shattori-criepi/omk/docs/design-principles.md

# 設計原則

## 1. この文書の目的

OMKは、一般的なWebアプリよりもハードウェア、通信、設置環境、長期運用の影響を強く受けます。本書は、個別の技術選定より長く維持する設計原則を定義します。

本書には長期的な設計方針も含み、すべてが現在の実装で満たされているわけではありません。実装済みの構成は[アーキテクチャ](developer/architecture.md)、保存形式・時刻・送信経路は[データ経路とMQTT仕様](developer/data-and-mqtt.md)を参照してください。現在は複数サービスで構成され、JSTのoffset付き時刻を保存し、Harvestへの送信はcollectorの保存完了と同期しません。Bルート固有CSVもJSONLと並行して保存します。

判断に迷った場合は、短期的にコード量が少ない方法よりも、次の優先順位を使います。

1. 計測データを失わない
2. 一部故障でも残りを動かす
3. 機器やベンダーを交換できる
4. 実機なしで開発・検証できる
5. 運用者が状態と原因を理解できる
6. 人間と生成AIが安全に変更できる

## 2. OMKの価値を維持する

OMKの価値は、多数のセンサを搭載すること自体ではありません。目的に応じて必要な計測機能を選択し、住宅への負担や設置コストを抑えながら長期間計測できることです。

### 原則

- センサ数を増やす前に、目的達成に必要かを確認する
- 設置作業、故障箇所、保守作業が増えることをコストとして扱う
- 構成は設定で選択できるようにする
- 使わない機能が他機能の起動を妨げないようにする
- UIは利用者に不要な操作を要求しない

## 3. モジュラーモノリスを優先する

OMKの初期・中期規模では、ネットワーク越しに分散した多数のサービスより、明確に分割された一つのアプリケーションの方が理解・検証・配備しやすいと判断します。

現在はこの判断基準に沿って、4つのComposeサービスとデバイス操作等のhost serviceに分割しています。この節は一つのプロセスへ統合済みであることを意味しません。

### 守ること

- モジュールごとに公開APIを定義する
- 他モジュールの内部ファイルを直接importしない
- 循環依存を作らない
- 一つの巨大な`utils`、`common`、`manager`へ責務を集めない
- コンテナ分割をコードの責務分割の代わりにしない
- コンテナを増やす場合は運用上の理由を記録する

### 分割の判断

別プロセス／別コンテナにする候補は、次の条件を持つものです。

- ランタイムが異なる
- 特殊なデバイス権限が必要
- 独立再起動に価値がある
- 障害やセキュリティを分離する必要がある

## 4. ハードウェアは交換可能なアダプタにする

### 原則

- ドメイン層はUSB、Bluetooth、Wi-SUN、GPIO、MQTTを知らない
- ベンダーSDKの型をアダプタ外へ出さない
- すべての実機ドライバにモックまたはシミュレータを用意する
- ドライバは共通`Measurement`を出力する
- ドライバの起動、停止、再接続、ヘルス確認を共通化する
- デバイス探索と計測処理を分ける

### 製品廃止への備え

機器の型番やSDKが廃止されることを例外ではなく通常のライフサイクルとして扱います。

- 型番をドメイン名やmetric名へ埋め込まない
- 設定でドライバ実装を選択する
- 通信プロトコルに対する契約テストを残す
- 実機がなくても再現できるサンプルデータを保存する
- 代替機器の評価結果は該当する`hardware/`またはコンポーネントREADMEへ記録し、確認済みの対応範囲は[対応機器](user/supported-devices.md)へ反映する
- 特定ベンダー機能へ依存する場合は理由と代替案を記録する

## 5. 取得と保存を分離し、JSONLを一次保存にする

各データ取得処理はMQTTへpublishし、汎用collectorがJSONLへ一次保存する。JSONLへの保存ではセンサ別の列定義へ展開せずpayloadを保持する。ただし現行collectorは保存前のBLE経路選択と、表示用latest cacheの抽出・互換出力も担う。JSONLは最終分析形式ではなく、CSV、分析、可視化、DB化、外部送信の入力となる生の保存形式である。

```text
Data acquisition
        ↓
MQTT internal data bus
        ↓
Generic collector
        ↓
JSONL primary storage
        ↓
CSV / analysis / visualization / external delivery
```

### 原則

- 取得と保存を分離し、MQTTを内部データバスとして使う
- topicは`omk/<device_id>/<data_type>`を基本とする
- collectorは`omk/#`を購読し、受信時刻・topic・payload等を保存する
- payloadの測定項目が増減してもcollectorを変更しない
- センサ固有の処理をcollectorへ持ち込まない
- CSVは一次保存ではなく、JSONLから生成する派生データとする

## 6. オフラインを通常状態として設計する

LTE、Wi-Fi、クラウド、MQTTは一時的に切断されます。通信断を例外処理だけで済ませず、通常運用の一部として設計します。

### 原則

- 外部送信より先にローカル保存する
- Outbox方式で未送信データを管理する
- 再送は指数バックオフと上限付きジッタを用いる
- 再送しても重複処理されない識別子を付ける
- キュー容量、ディスク使用量、最古未送信時刻を監視する
- 復旧後に自動追いつきできる
- 通信断中もUIで現在値と状態を確認できる

## 7. 一部故障を全体障害にしない

### 原則

- 一つのセンサ初期化失敗でプロセス全体を終了しない
- ドライバごとに状態と再接続処理を持つ
- 連続失敗をレート制限してログ出力する
- 依存していない機能は継続する
- 必須デバイスと任意デバイスを設定で区別する
- プロセス再起動に頼る前にコンポーネント単位で復旧する

### 状態の例

```text
starting → healthy → degraded → reconnecting → healthy
                     └──────────→ failed
```

`failed`でも、他コンポーネントが動作可能ならシステム全体のlivenessは維持します。

## 8. Raspberry Pi OSとコンテナの境界を保つ

DockerはすべてのOS設定を隠すためのものではありません。周辺機器を安定して使うため、ホストOSの責務を明確に残します。

### ホストOSへ置くもの

- カーネルドライバ
- Bluetoothデーモン
- LTE接続管理
- USB・シリアル認識
- udevルール
- ディスプレイ設定
- 時刻同期
- OS更新・再起動・電源管理
- Bルート通信（USBシリアル、PANA、認証）を実行するsystemdサービス

### コンテナへ置くもの

- 計測プロトコル
- データ変換
- 保存・送信
- API・UI
- ログ・ヘルスチェック
- モック・自動テスト

Bルート通信そのものは当面コンテナ化しない。Bルート取得値はMQTTへpublishし、他のセンサと同じ汎用collectorとJSONL一次保存へ集約する。既存の専用保存は、並行運用の検証が完了するまで維持する。

### 禁止事項

- 理由なく`privileged: true`を使う
- ホストのルートファイルシステムを広範囲にマウントする
- デバイスパスをコードへ直書きする
- ホスト設定変更をアプリ起動時に暗黙実行する

## 9. 設定とコードを分ける

設置場所ごとの差異は、原則としてコードの分岐ではなく設定で表現します。

### 設定に置くもの

- 有効なドライバ
- デバイスパス・Bluetoothアドレス
- 計測間隔
- サイト／デバイス識別子
- 保存期間
- 送信先種別とバッチサイズ
- UI表示項目
- ログレベル

### コードに置かないもの

- BルートID・パスワード
- APIキー
- SIM・利用者・設置場所を特定する秘密値
- 実在住宅固有の設定

設定は起動時にスキーマ検証し、誤りを分かりやすく報告します。

## 10. 時刻・単位・識別子を曖昧にしない

IoTデータでは、値そのものよりメタデータの曖昧さが後から大きな問題になります。

### 時刻

- 内部保存・通信はUTC
- UI表示時にタイムゾーン変換
- 観測時刻と受信時刻を区別
- NTP同期状態を監視
- 時計が不正なデータには品質フラグを付ける

### 単位

- 値と単位をセットで扱う
- 単位変換は正規化層で行う
- 変数名だけに単位情報を持たせない
- 同じmetricでは同じ基準単位を使う

### 識別子

- 表示名を主キーにしない
- `siteId`、`deviceId`、`sensorId`を分ける
- MACアドレス等の変更可能値へ過度に依存しない
- 再設置・機器交換時の識別方針を明示する

## 11. セキュリティとプライバシーを後付けにしない

住宅内の電力・環境データは、生活パターンを推定できる可能性があります。

### 原則

- 必要なデータだけを収集する
- 収集目的、保持期間、送信先を設定・文書で明示する
- 本番認証情報をGitへ入れない
- ログへ秘密値や生データを過剰に出さない
- MQTT、UI、APIの公開範囲を最小化する
- 不要になったデータを削除できる
- テストデータは実住宅データを匿名化または合成する
- 外部送信を停止してもローカル計測が動くようにする

## 12. 可観測性を機能として設計する

「動いているか分からない」は運用障害です。

最低限、次を確認できるようにします。

- 各ドライバの状態
- 最終計測時刻
- 最終保存時刻
- 未送信件数と最古データ
- ディスク使用量
- MQTT接続状態
- LTE／外部送信状態
- アプリと設定のバージョン
- 最後に発生した主要エラー

ログは人間が読むメッセージだけでなく、機械で集計できる構造を持たせます。

## 13. テスト可能性を設計要件にする

### 必須テスト層

1. **単体テスト**: ドメイン、変換、バリデーション、再送判断
2. **契約テスト**: ドライバ、MQTT payload、API、保存ポート
3. **統合テスト**: broker、DB、Outbox、コンテナ間通信
4. **実機スモークテスト**: Raspberry Piと周辺機器
5. **長時間試験**: 通信断、再起動、ディスク逼迫、センサ切断

### 原則

- 時刻、乱数、ネットワークを直接参照せず注入可能にする
- 実機がないとテストできないロジックを最小化する
- 不具合修正には再現テストを追加する
- サンプルデータは小さく、意味が分かる名前を付ける
- 実機テストを単体テストの代用にしない

## 14. AIフレンドリーなコードベースにする

Codex等の生成AIにコード変更を任せる場合も、変更に必要な仕様と判断理由をリポジトリの文書に残します。

### 文書

- `README.md`は入口と全体像
- `docs/developer/architecture.md`は境界と依存規則
- `hardware/`と各コンポーネントREADMEは実機差分
- `docs/developer/development.md`は作業手順
- 重要判断はADRまたは文書の判断表へ残す

### コード

- 役割が分かる名前を使う
- 1ファイルに複数の無関係な責務を置かない
- 暗黙のグローバル状態を避ける
- 型とスキーマを明示する
- エラーを握りつぶさない
- コメントは「何をしているか」より「なぜ必要か」を書く
- TODOには理由、完了条件、関連Issueを付ける

### AIへ任せる変更の単位

- 1回の変更で一つの目的に絞る
- 先に関連文書と契約を読ませる
- 変更後にテスト、lint、型チェックを実行させる
- 変更した契約と文書を列挙させる
- 不明点を勝手に仕様化させない

## 15. 命名規則

### ファイル・ディレクトリ

- Markdown、設定、一般ファイル: `kebab-case`
- TypeScriptソース: リポジトリで一貫した方式を使う。初期案は`kebab-case.ts`
- テスト: `*.test.ts`または`*.spec.ts`のどちらかに統一
- 環境変数: `UPPER_SNAKE_CASE`

### TypeScript

- 型、interface、class: `PascalCase`
- 関数、変数、プロパティ: `camelCase`
- 定数: 原則`camelCase`。環境変数名やプロトコル定数のみ`UPPER_SNAKE_CASE`
- boolean: `is`、`has`、`can`、`should`等で始める
- ポート: 役割名を付ける。例`MeasurementRepository`、`UploadTarget`
- 実装: 技術名＋役割。例`SqliteMeasurementRepository`、`SoracomUploadTarget`

### ID

- `siteId`: 設置単位
- `deviceId`: 物理・論理デバイス単位
- `sensorId`: デバイス内の計測点
- `measurementId`: 計測レコード単位

「id」だけの変数を広いスコープで使いません。

## 16. 依存ライブラリの扱い

- 標準機能で十分な場合は依存を増やさない
- ハードウェアSDKはアダプタ内に閉じ込める
- バージョンをlockfileで固定する
- 非推奨・保守停止ライブラリを新規採用しない
- 依存追加時は目的、代替、ライセンス、Raspberry Pi対応を確認する
- ARMアーキテクチャでビルド可能かをCIまたは実機で確認する

## 17. 設計原則から外れる場合

設計原則は絶対的な禁止事項ではありません。外れる必要がある場合は、次を記録します。

- 解決したい問題
- 採用した例外
- 代替案
- 影響範囲
- 元へ戻す条件
- テスト方法

「急いでいた」「動いたから」だけを理由に恒久化しません。
