shattori-criepi/omk/firmware/esp32/omk-node/src/node_protocol.h

#pragma once

#include <stdint.h>

#define OMK_NODE_PROTOCOL_VERSION 1U

#define OMK_NODE_PROVISIONING_STATE_UNREGISTERED 0U
#define OMK_NODE_PROVISIONING_STATE_PROVISIONED 1U
#define OMK_NODE_PROVISIONING_STATE_REGISTERED 2U

#define OMK_NODE_CAPABILITY_BLE_SCAN (1U << 0)
#define OMK_NODE_CAPABILITY_SEN66 (1U << 1)

/* Advertises firmware support, not whether a supported sensor is attached. */
#define OMK_NODE_CAPABILITIES (OMK_NODE_CAPABILITY_BLE_SCAN | OMK_NODE_CAPABILITY_SEN66)
