shattori-criepi/omk/services/broute-meter/tests/unit/test_resilience.py

"""連続失敗と再接続処理の単体テスト。"""

from __future__ import annotations

from collections import deque
from datetime import UTC, datetime

import pytest

from broute_meter.adapter import AdapterCommunicationError, AdapterOperationCancelled
from broute_meter.models import InstantaneousPowerReading
from broute_meter.resilience import (
    MeasurementCancelledError,
    MeasurementUnavailableError,
    RecoveringMeterReader,
)


class CommunicationFailure(RuntimeError):
    pass


class ScriptedMeter:
    def __init__(self, outcomes: list[int | Exception]) -> None:
        self.outcomes = deque(outcomes)

    def get_instantaneous_power(self) -> InstantaneousPowerReading:
        outcome = self.outcomes.popleft()
        if isinstance(outcome, Exception):
            raise outcome
        return InstantaneousPowerReading(
            datetime(2026, 7, 25, tzinfo=UTC),
            outcome,
        )

    def get_cumulative_energy(self):
        raise AssertionError("このテストでは使用しません")


class StopEvent:
    def __init__(self, stopped: bool = False) -> None:
        self.stopped = stopped
        self.waits: list[float | None] = []

    def wait(self, timeout: float | None = None) -> bool:
        self.waits.append(timeout)
        return self.stopped


def _recovering(
    meter: ScriptedMeter,
    reconnect,
    stop_event: StopEvent,
    *,
    threshold: int = 2,
) -> RecoveringMeterReader:
    return RecoveringMeterReader(
        meter,
        reconnect,
        recoverable_exceptions=(CommunicationFailure,),
        reconnect_after_consecutive_failures=threshold,
        reconnect_wait_seconds=30,
        stop_event=stop_event,
    )


def test_success_resets_consecutive_failure_count() -> None:
    meter = ScriptedMeter(
        [
            CommunicationFailure("first"),
            100,
            CommunicationFailure("after success"),
        ]
    )
    reconnect_calls = 0

    def reconnect() -> ScriptedMeter:
        nonlocal reconnect_calls
        reconnect_calls += 1
        return ScriptedMeter([200])

    recovering = _recovering(meter, reconnect, StopEvent())

    with pytest.raises(MeasurementUnavailableError):
        recovering.get_instantaneous_power()
    assert recovering.get_instantaneous_power().net_power_w == 100
    with pytest.raises(MeasurementUnavailableError):
        recovering.get_instantaneous_power()
    assert reconnect_calls == 0


def test_threshold_reopens_connection_and_retries_measurement() -> None:
    meter = ScriptedMeter(
        [
            CommunicationFailure("first"),
            CommunicationFailure("second"),
        ]
    )
    reconnect_calls = 0

    def reconnect() -> ScriptedMeter:
        nonlocal reconnect_calls
        reconnect_calls += 1
        return ScriptedMeter([321])

    stop_event = StopEvent()
    recovering = _recovering(meter, reconnect, stop_event)

    with pytest.raises(MeasurementUnavailableError):
        recovering.get_instantaneous_power()
    reading = recovering.get_instantaneous_power()

    assert reading.net_power_w == 321
    assert reconnect_calls == 1
    assert stop_event.waits == [30]


def test_shutdown_interrupts_reconnect_wait() -> None:
    meter = ScriptedMeter([CommunicationFailure("stop")])
    reconnect_calls = 0

    def reconnect() -> ScriptedMeter:
        nonlocal reconnect_calls
        reconnect_calls += 1
        return ScriptedMeter([1])

    recovering = _recovering(
        meter,
        reconnect,
        StopEvent(stopped=True),
        threshold=1,
    )

    with pytest.raises(MeasurementCancelledError, match="終了要求"):
        recovering.get_instantaneous_power()
    assert reconnect_calls == 0


@pytest.mark.parametrize("measurement", ["instantaneous", "cumulative"])
def test_adapter_shutdown_cancellation_is_not_counted_as_missing(
    measurement: str,
) -> None:
    class CancelledMeter:
        def get_instantaneous_power(self) -> InstantaneousPowerReading:
            raise AdapterOperationCancelled("shutdown")

        def get_cumulative_energy(self) -> object:
            raise AdapterOperationCancelled("shutdown")

    recovering = RecoveringMeterReader(
        CancelledMeter(),  # type: ignore[arg-type]
        lambda: pytest.fail("reconnect must not run"),
        recoverable_exceptions=(AdapterOperationCancelled, CommunicationFailure),
        reconnect_after_consecutive_failures=1,
        reconnect_wait_seconds=30,
        stop_event=StopEvent(),
    )

    operation = (
        recovering.get_instantaneous_power
        if measurement == "instantaneous"
        else recovering.get_cumulative_energy
    )
    with pytest.raises(MeasurementCancelledError, match="終了要求"):
        operation()
    assert recovering._consecutive_failures == 0


def test_reconnect_operation_shutdown_cancellation_is_not_missing() -> None:
    meter = ScriptedMeter([CommunicationFailure("first")])

    class CancelledMeter:
        def get_instantaneous_power(self) -> InstantaneousPowerReading:
            raise AdapterOperationCancelled("shutdown")

        def get_cumulative_energy(self) -> object:
            raise AssertionError("not used")

    recovering = RecoveringMeterReader(
        meter,
        lambda: CancelledMeter(),  # type: ignore[arg-type]
        recoverable_exceptions=(CommunicationFailure, AdapterOperationCancelled),
        reconnect_after_consecutive_failures=1,
        reconnect_wait_seconds=0,
        stop_event=StopEvent(),
    )

    with pytest.raises(MeasurementCancelledError, match="終了要求"):
        recovering.get_instantaneous_power()
    assert recovering._consecutive_failures == 0


def test_adapter_communication_failure_remains_missing_and_increments_count() -> None:
    class FailingMeter:
        def get_instantaneous_power(self) -> InstantaneousPowerReading:
            raise AdapterCommunicationError("serial failure")

        def get_cumulative_energy(self) -> object:
            raise AssertionError("not used")

    recovering = RecoveringMeterReader(
        FailingMeter(),  # type: ignore[arg-type]
        lambda: pytest.fail("reconnect threshold was not reached"),
        recoverable_exceptions=(AdapterCommunicationError, AdapterOperationCancelled),
        reconnect_after_consecutive_failures=2,
        reconnect_wait_seconds=30,
        stop_event=StopEvent(),
    )

    with pytest.raises(MeasurementUnavailableError, match="瞬時電力を取得できません"):
        recovering.get_instantaneous_power()
    assert recovering._consecutive_failures == 1
