shattori-criepi/omk/services/broute-meter/tests/unit/test_interval_energy.py

"""30分買電・売電量算出の単体テスト。"""

from __future__ import annotations

from datetime import UTC, datetime, timedelta
from decimal import Decimal

import pytest

from broute_meter.models import CumulativeEnergyReading
from broute_meter.processing import QualityStatus, calculate_interval_energy


def _reading(
    metered_at: datetime,
    forward: str,
    reverse: str | None,
) -> CumulativeEnergyReading:
    return CumulativeEnergyReading(
        metered_at=metered_at,
        received_at=metered_at,
        forward_raw=0,
        reverse_raw=0 if reverse is not None else None,
        forward_total_kwh=Decimal(forward),
        reverse_total_kwh=Decimal(reverse) if reverse is not None else None,
    )


@pytest.mark.parametrize(
    ("previous_values", "current_values", "expected_import", "expected_export"),
    [
        (("100.00", "20.00"), ("100.35", "20.12"), "0.35", "0.12"),
        (("100.00", "20.00"), ("100.35", "20.00"), "0.35", "0.00"),
        (("100.00", "20.00"), ("100.00", "20.12"), "0.00", "0.12"),
        (("0.1", "0.2"), ("0.3", "0.5"), "0.2", "0.3"),
    ],
)
def test_calculate_normal_interval_without_float_rounding(
    previous_values: tuple[str, str],
    current_values: tuple[str, str],
    expected_import: str,
    expected_export: str,
) -> None:
    start = datetime(2026, 7, 25, 9, 0, tzinfo=UTC)
    result = calculate_interval_energy(
        _reading(start, *previous_values),
        _reading(start + timedelta(minutes=30), *current_values),
    )
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
